MrKnowledge9039/KnowledgeBoard/firmware/boot.py

import board

from kmk.bootcfg import bootcfg

bootcfg(
    sense=board.GP0,  # column
    source=board.GP8, # row
    midi=False,
    mouse=False,
    storage=False,
    usb_id={'manufacturer': 'MrKnowledge', 'product': 'KnowledgeBoard'},
)
